udu3324/stm32pe-midi/cad/key/v3.png

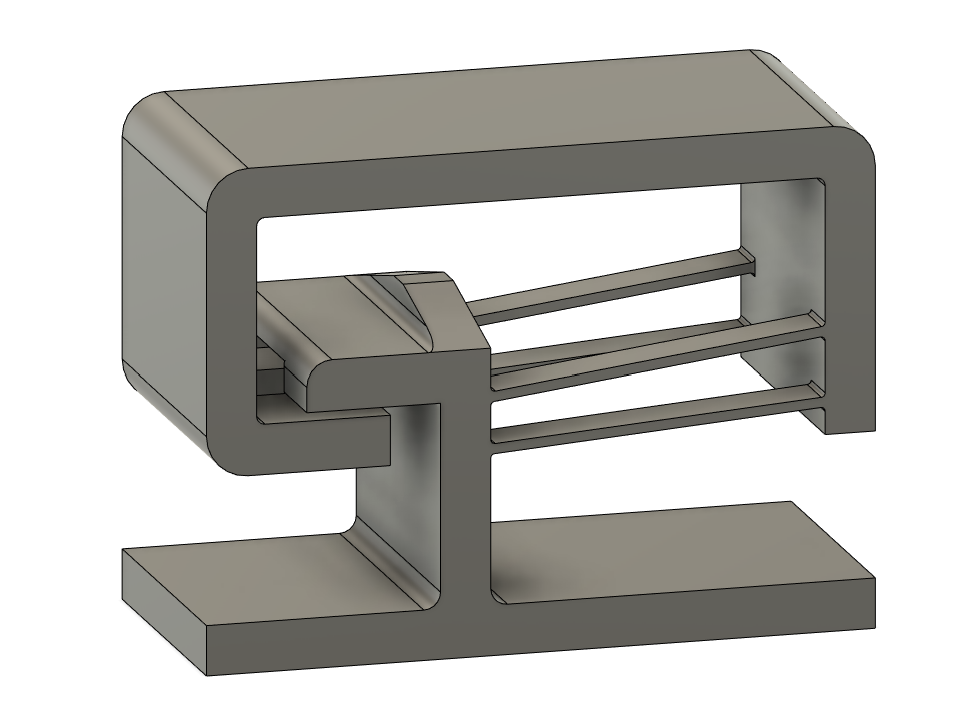
cad/key/v3.png
