udu3324/stm32pe-midi/cad/stm32pe-midi case v42.png

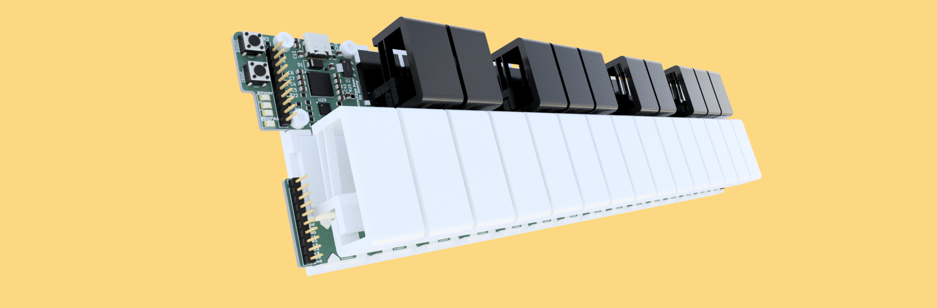
cad/stm32pe-midi case v42.png
