udu3324/stm32pe-midi/production/jlcpcb info/jlcpcb picked parts.png

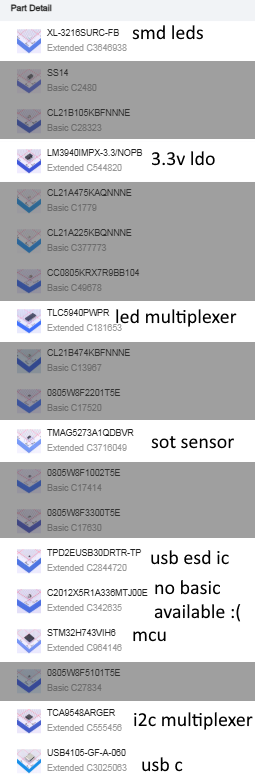
production/jlcpcb info/jlcpcb picked parts.png
