udu3324/stm32pe-midi/pcb/stm32pe_midi/sensor_line_v2.dxf

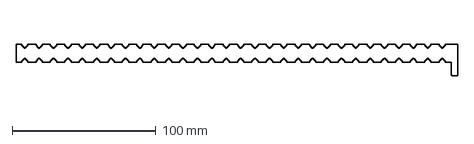
[picture p24: CAD file, 2025-06-25]
pcb/stm32pe_midi/sensor_line_v2.dxf
307.0 x 22.0 mm
