udu3324/stm32pe-midi/cad/small key/16.stl

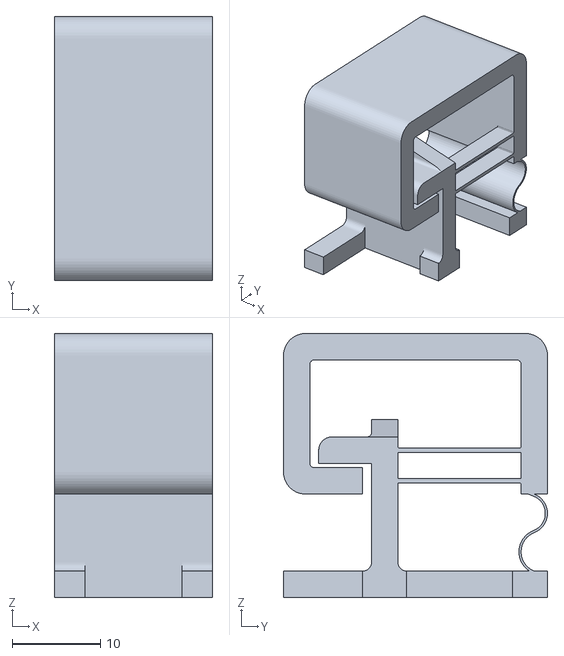
[picture p25: CAD file, 2025-06-13]
cad/small key/16.stl
18.0 x 30.0 x 30.0
