udu3324/stm32pe-midi/firmware/stm32pe_midi/Core/Inc/mpe.h

#ifndef MPE_H
#define MPE_H

void MPE_Init(void);

void MPE_Send_Note_On(uint8_t note, uint8_t velocity);

void MPE_Send_Note_Off(uint8_t note);

void MPE_Send_Pitch_Bend(uint8_t note, int16_t bend_val);

void MPE_Send_Aftertouch(uint8_t note, uint8_t pressure);

#endif
